virginienokill/camera-obscura/assets/img/file.dxf.png

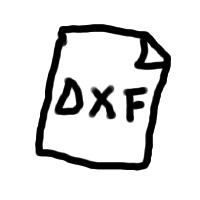
assets/img/file.dxf.png
