virginienokill/camera-obscura/assets/img/file.png

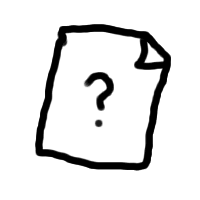
assets/img/file.png
