virginienokill/camera-obscura/contenu/dessins/dessin_camera_camion.png

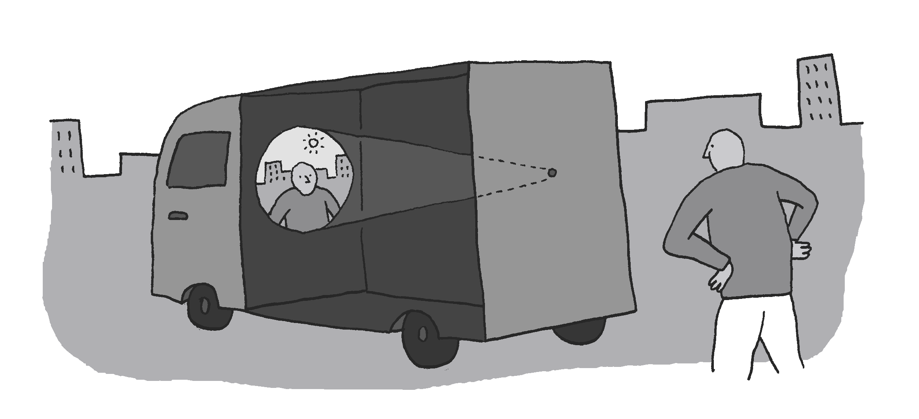
contenu/dessins/dessin_camera_camion.png
