virginienokill/camera-obscura/contenu/dessins/macaron_thumb_5.png

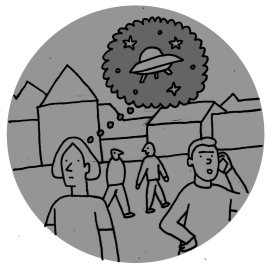
contenu/dessins/macaron_thumb_5.png
