virginienokill/camera-obscura/contenu/photos/apo_nikkor_9_610mm_1.jpg

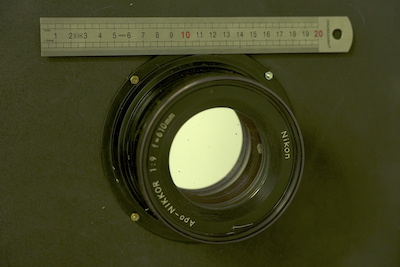
contenu/photos/apo_nikkor_9_610mm_1.jpg
