virginienokill/camera-obscura/contenu/photos/les_yeux_dans_le_dos_5.jpg

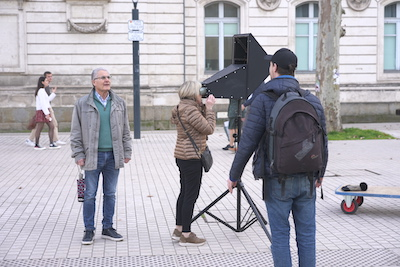
contenu/photos/les_yeux_dans_le_dos_5.jpg
