virginienokill/camera-obscura/contenu/plans/collage-soufflet-patrons.png

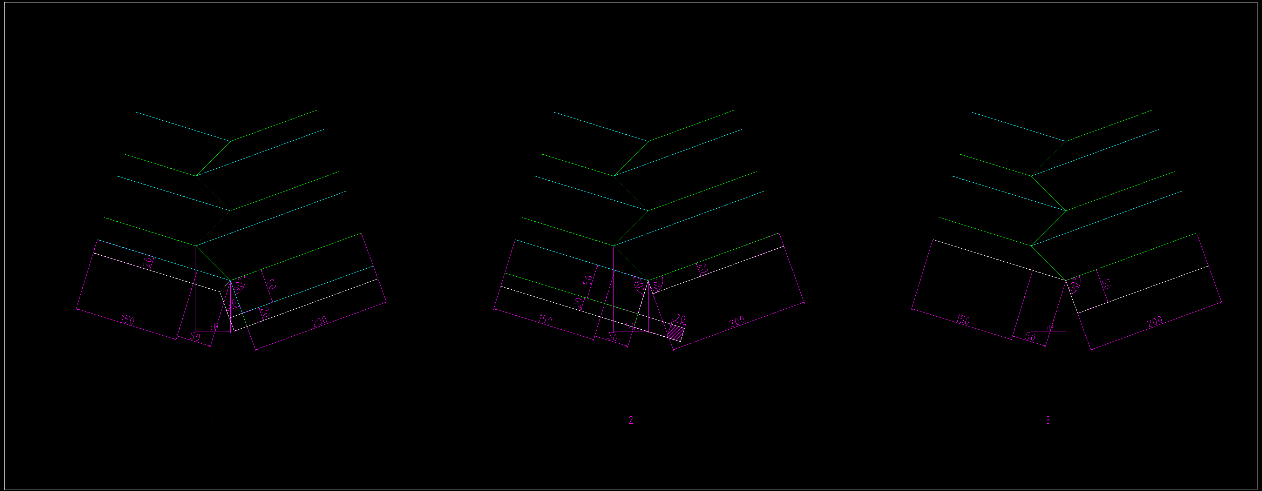
contenu/plans/collage-soufflet-patrons.png
