virginienokill/camera-obscura/contenu/plans/dim_chambre_antotype_ultralight.jpeg

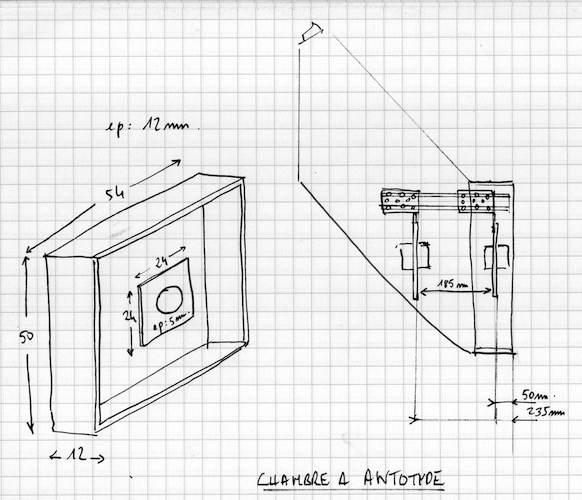
contenu/plans/dim_chambre_antotype_ultralight.jpeg
