virginienokill/camera-obscura/contenu/plans/dim_chambre_grand_format_ultralight.jpeg

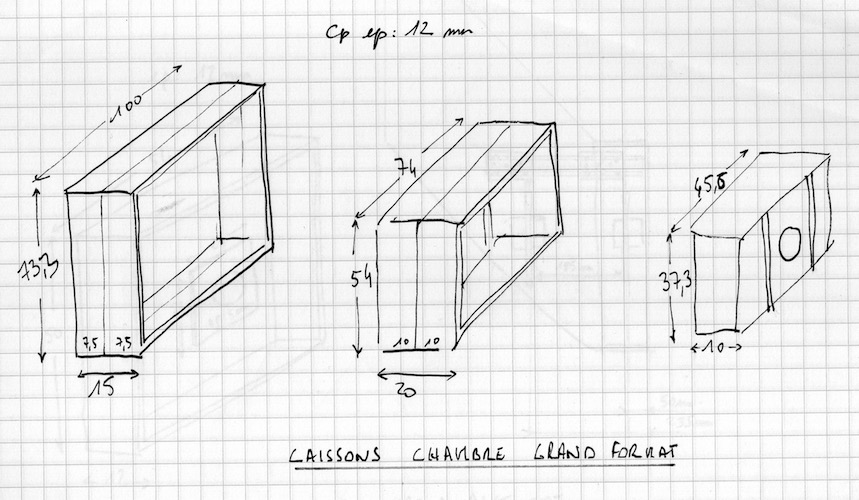
contenu/plans/dim_chambre_grand_format_ultralight.jpeg
