virginienokill/camera-obscura/contenu/plans/dim_chambre_remorque_ultralight.jpeg

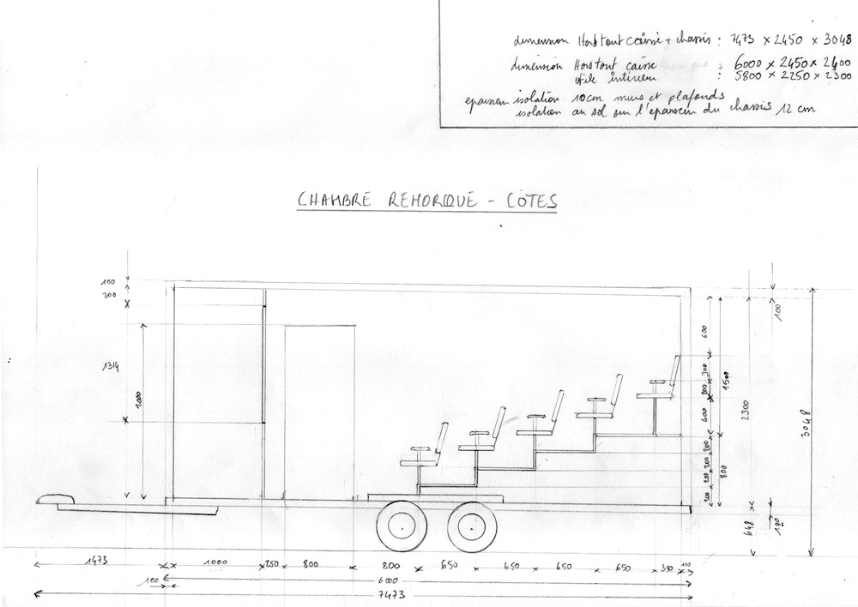
contenu/plans/dim_chambre_remorque_ultralight.jpeg
