virginienokill/camera-obscura/contenu/plans/dim_chambre_remorque_v2.jpeg

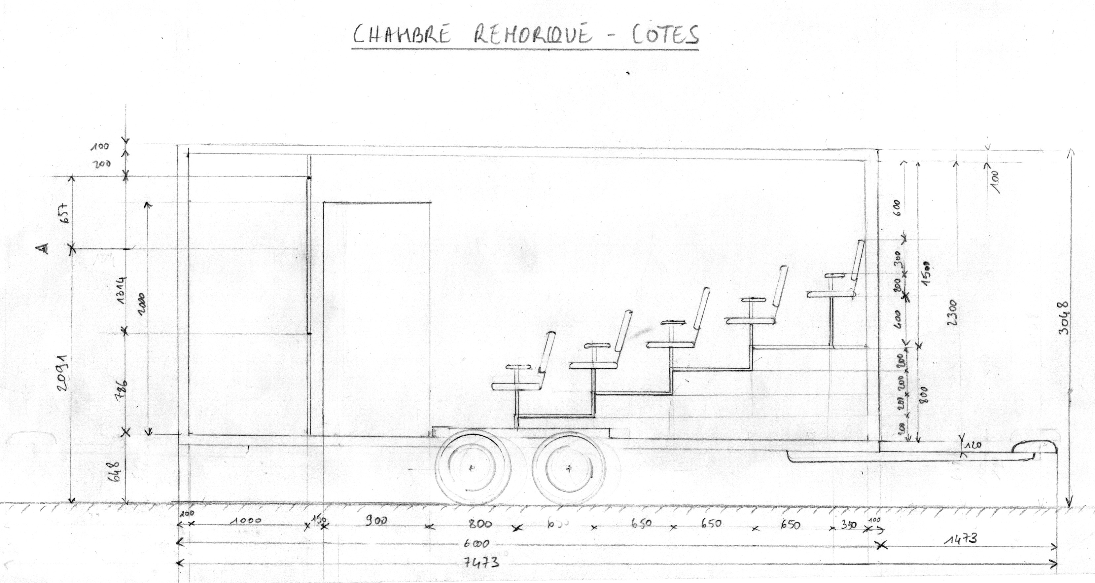
contenu/plans/dim_chambre_remorque_v2.jpeg
