virginienokill/camera-obscura/contenu/plans/dim_panneau_sprinter_ultralight.jpeg

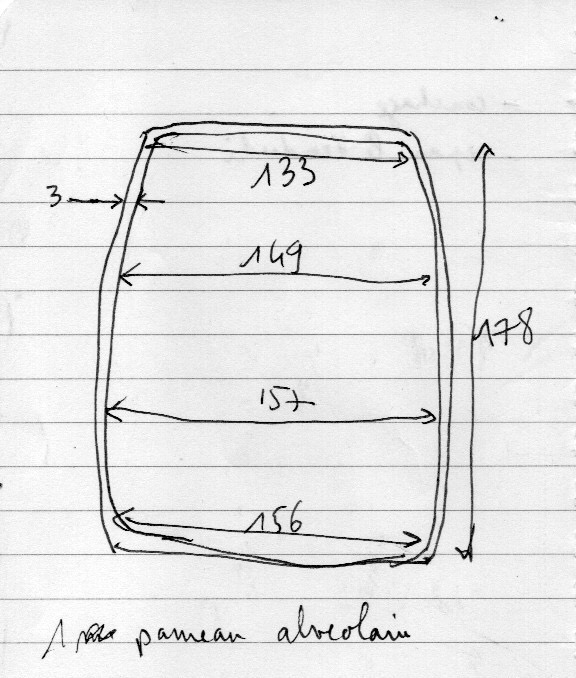
contenu/plans/dim_panneau_sprinter_ultralight.jpeg
