virginienokill/camera-obscura/contenu/plans/plans_modules.png

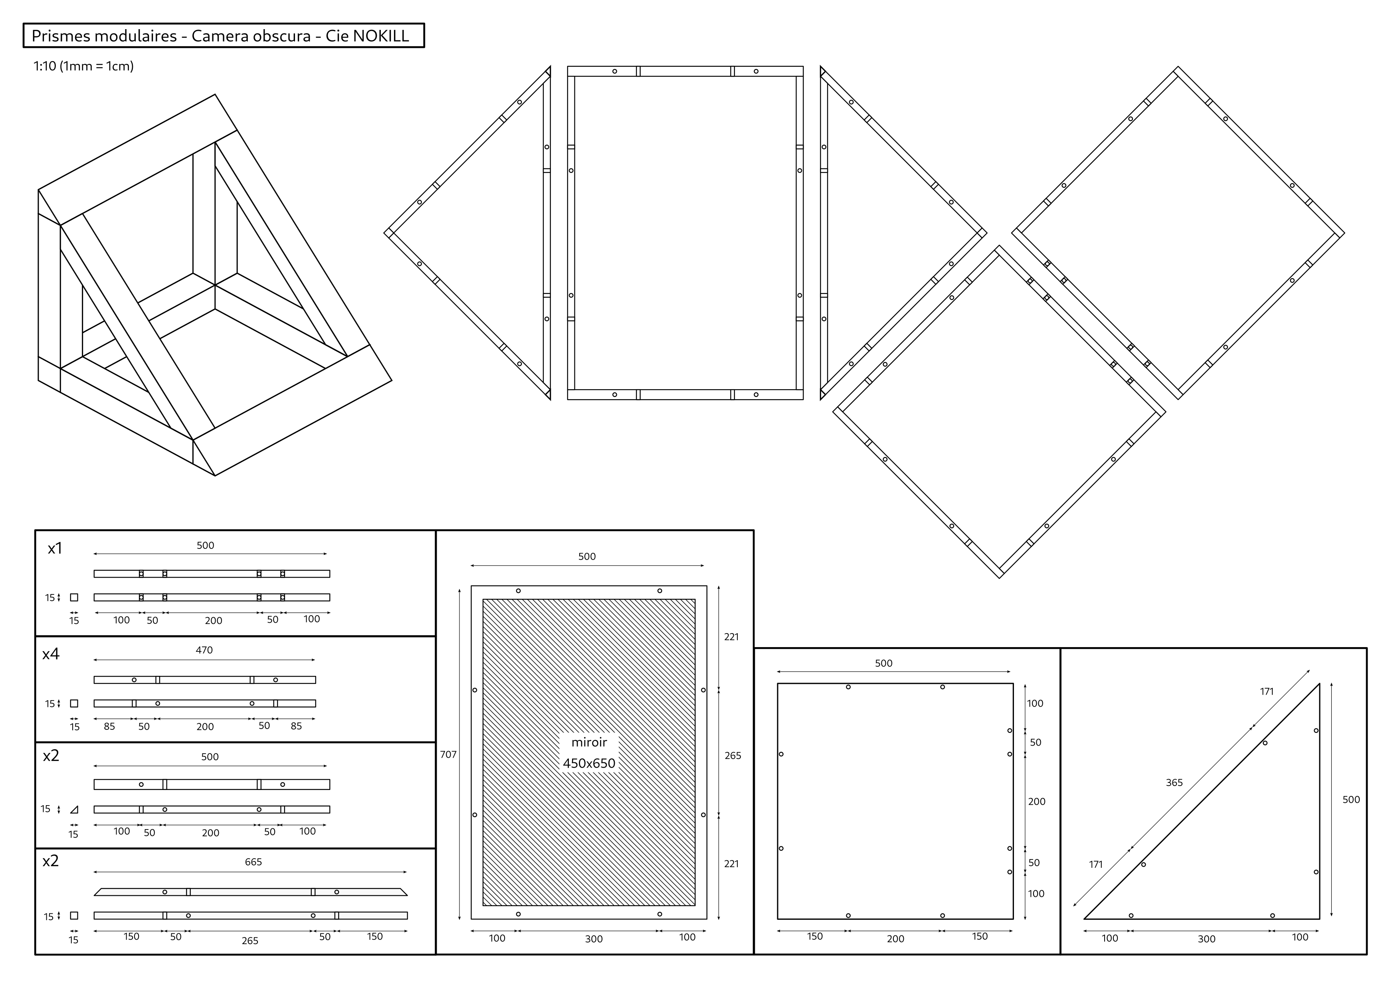
contenu/plans/plans_modules.png
