virginienokill/camera-obscura/contenu/plans/proto_00.jpg

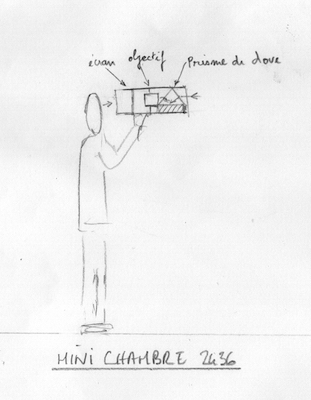
contenu/plans/proto_00.jpg
