virginienokill/camera-obscura/docs/macarons/6.png

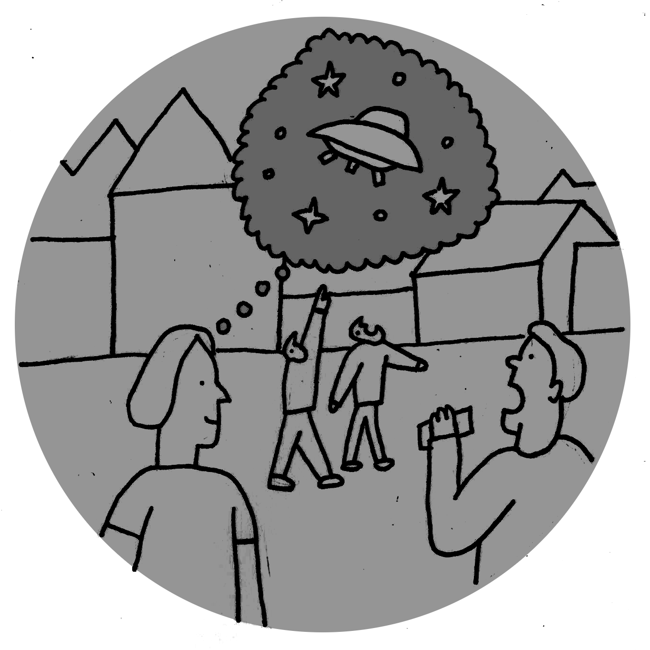
docs/macarons/6.png
